Miceuz/yagi-uda-3d-print/Mechanical/gamma-match-node-threads-Exploded Slice1.amf

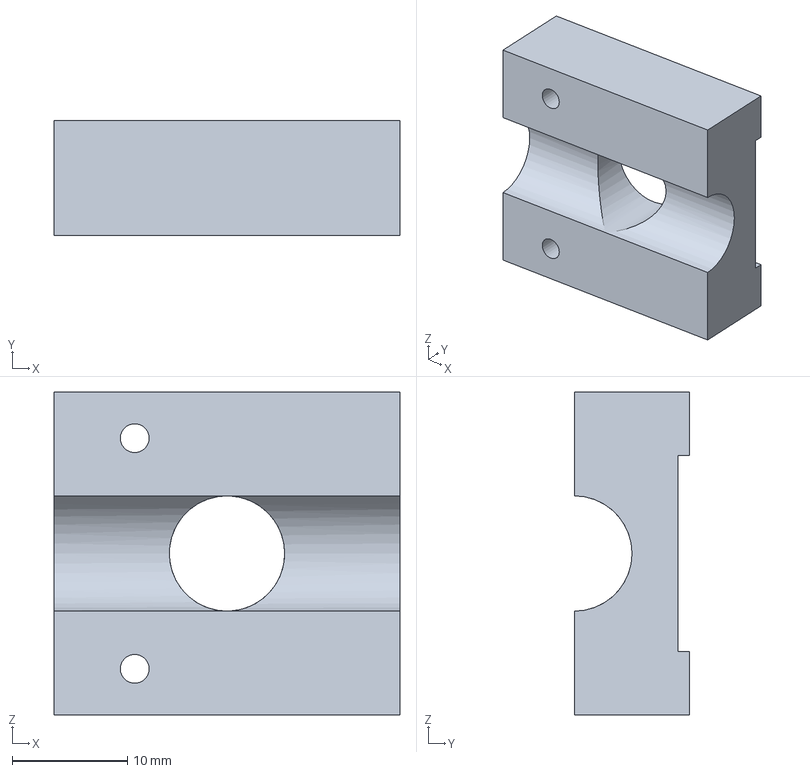
[picture p18: CAD file, 2023-11-08]
Mechanical/gamma-match-node-threads-Exploded Slice1.amf
30.0 x 10.0 x 28.0 mm
