Miceuz/yagi-uda-3d-print/Mechanical/Holder.FCStd

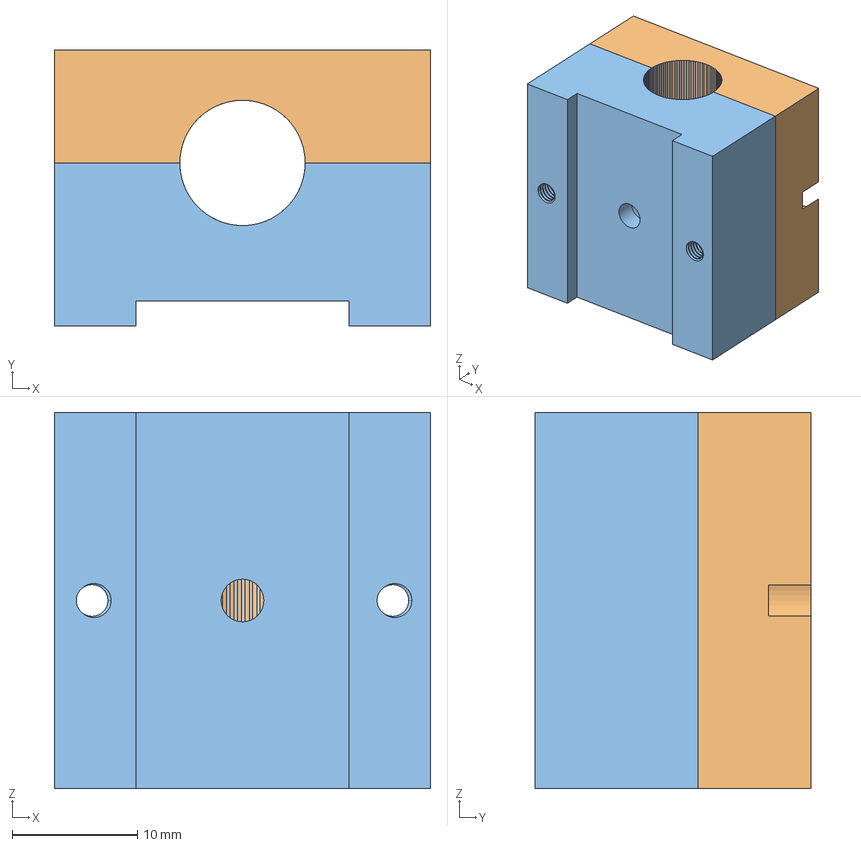
[picture p19: CAD file, 2023-11-08]
Mechanical/Holder.FCStd
30.0 x 22.0 x 30.0 mm
Slice.0
Slice.1
