Miceuz/yagi-uda-3d-print/Mechanical/gamma-match-node-threads-Slice0.3mf

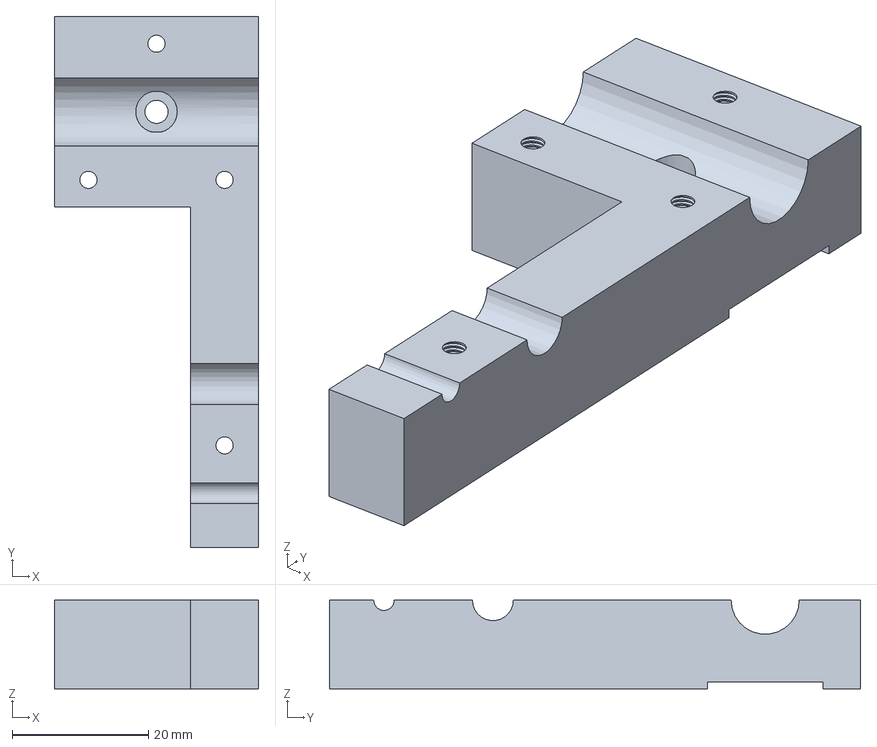
[picture p20: CAD file, 2023-11-08]
Mechanical/gamma-match-node-threads-Slice0.3mf
30.0 x 78.0 x 13.0 mm
