Miceuz/yagi-uda-3d-print/Mechanical/gamma-match-node-threads-Slice1.3mf

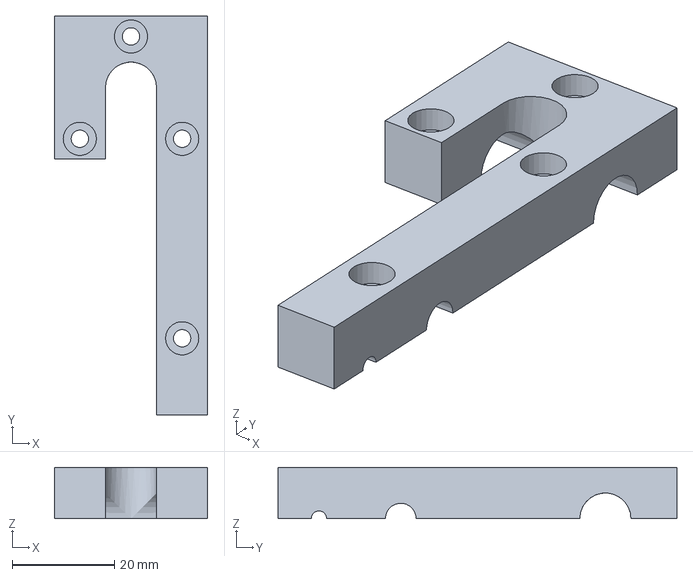
[picture p21: CAD file, 2023-11-08]
Mechanical/gamma-match-node-threads-Slice1.3mf
30.0 x 78.0 x 10.0 mm
