Miceuz/yagi-uda-3d-print/Mechanical/gamma-match-node-threads-Exploded Slice0.amf

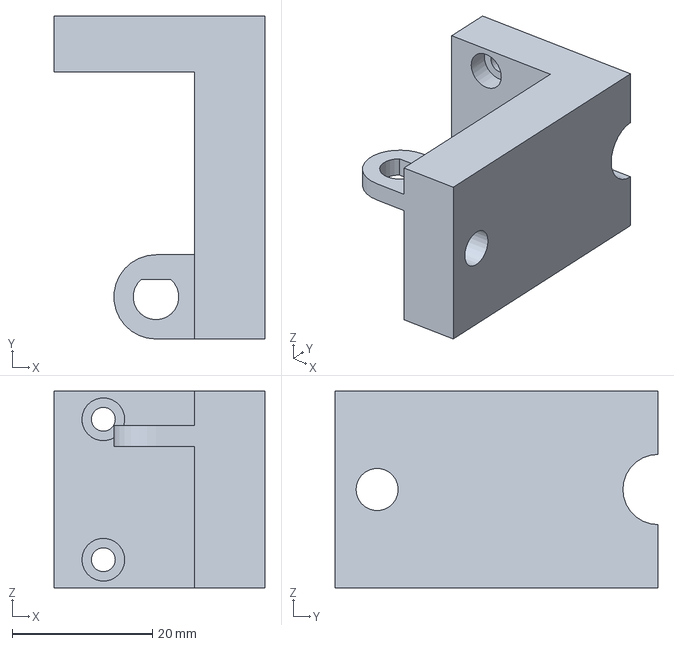
[picture p22: CAD file, 2023-11-08]
Mechanical/gamma-match-node-threads-Exploded Slice0.amf
30.0 x 46.0 x 28.0 mm
