Miceuz/yagi-uda-3d-print/Mechanical/gamma-slice1.3mf

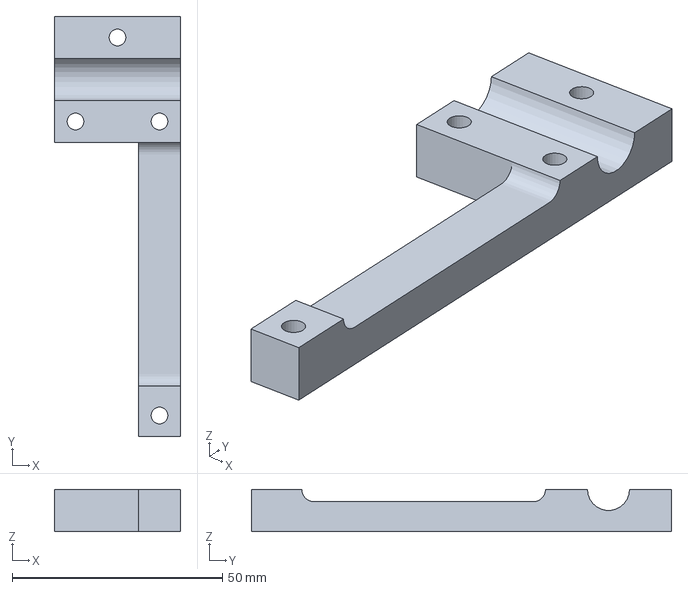
[picture p23: CAD file, 2023-11-08]
Mechanical/gamma-slice1.3mf
30.0 x 100.0 x 10.0 mm
